rhgndf/hfsdr/art/art_export/cropped.png

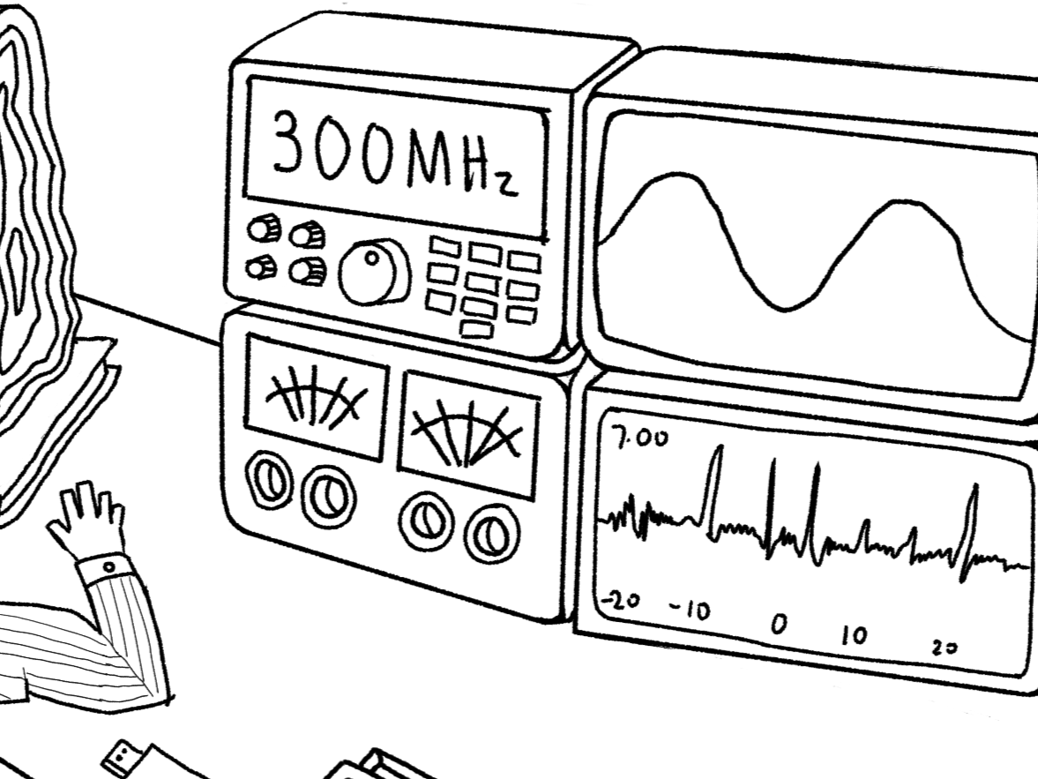
art/art_export/cropped.png
