rhgndf/hfsdr/hardware/screen docs/IMG_8584.JPG

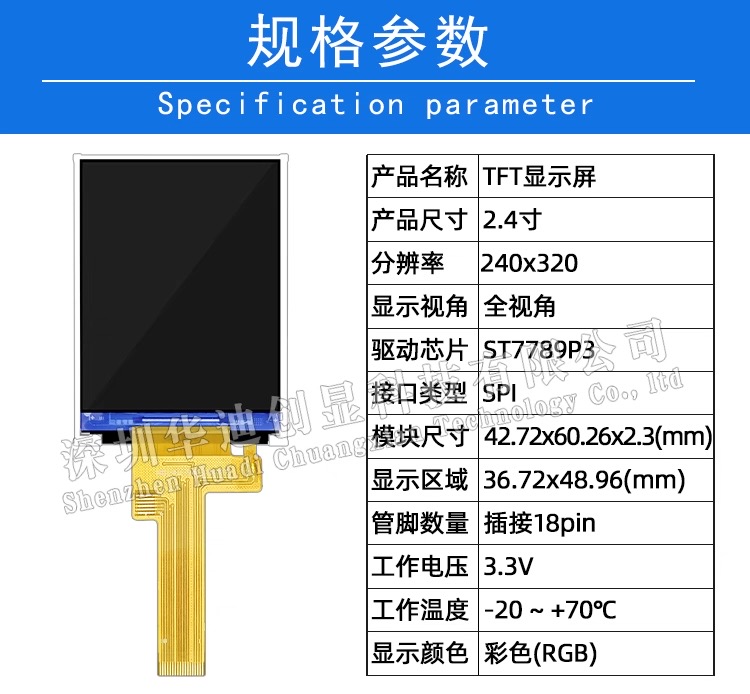
hardware/screen docs/IMG_8584.JPG
