rhgndf/hfsdr/hardware/screen docs/IMG_8585.JPG

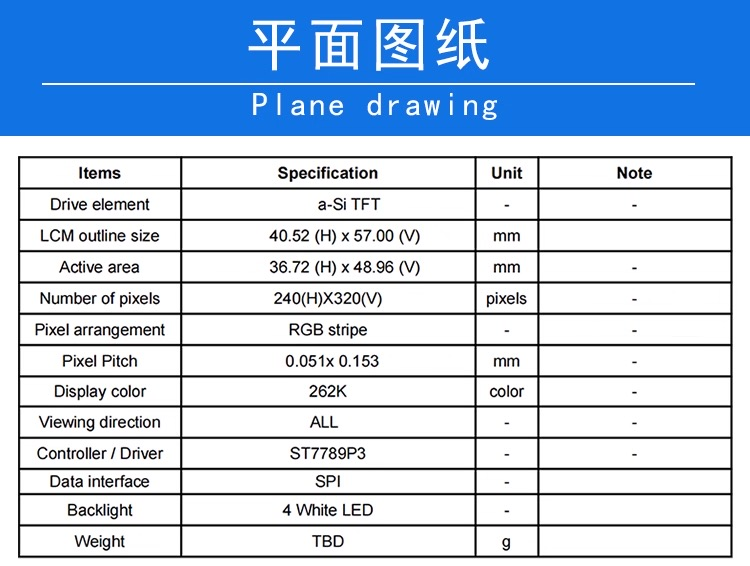
hardware/screen docs/IMG_8585.JPG
