rhgndf/hfsdr/hardware/screen docs/IMG_8586.JPG

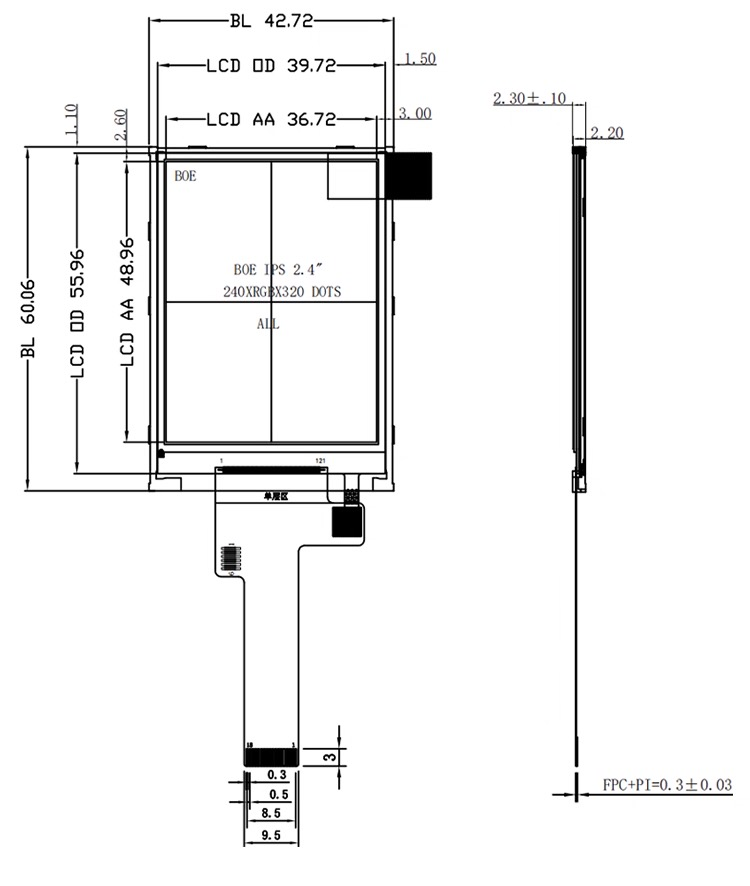
hardware/screen docs/IMG_8586.JPG
