rhgndf/hfsdr/hardware/screen docs/IMG_8587.JPG

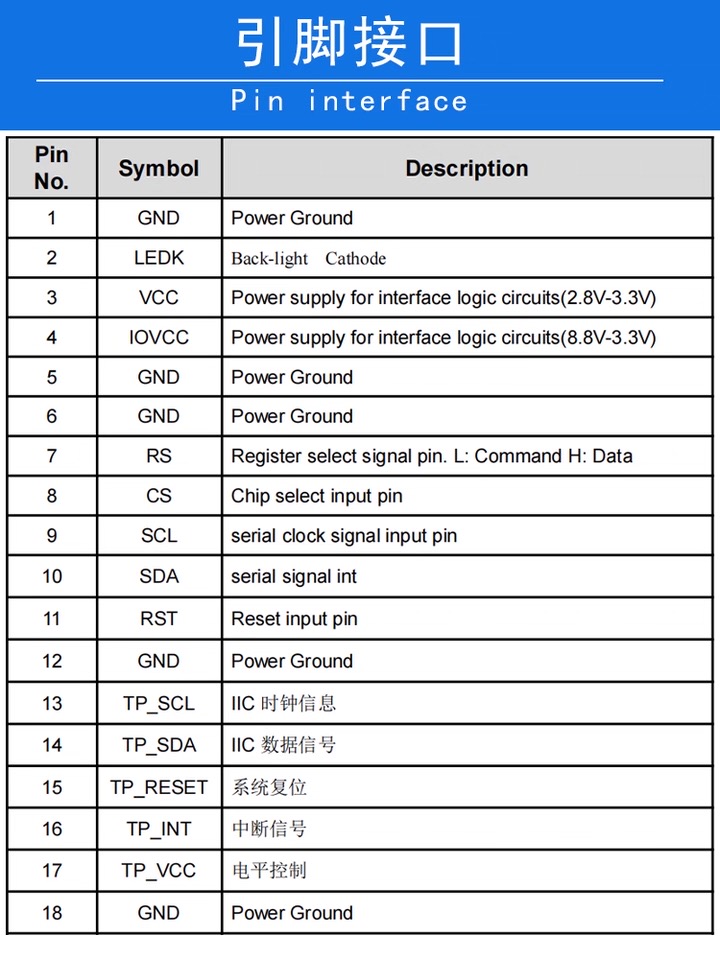
hardware/screen docs/IMG_8587.JPG
