rhgndf/hfsdr/hardware/screen docs/IMG_8588.JPG

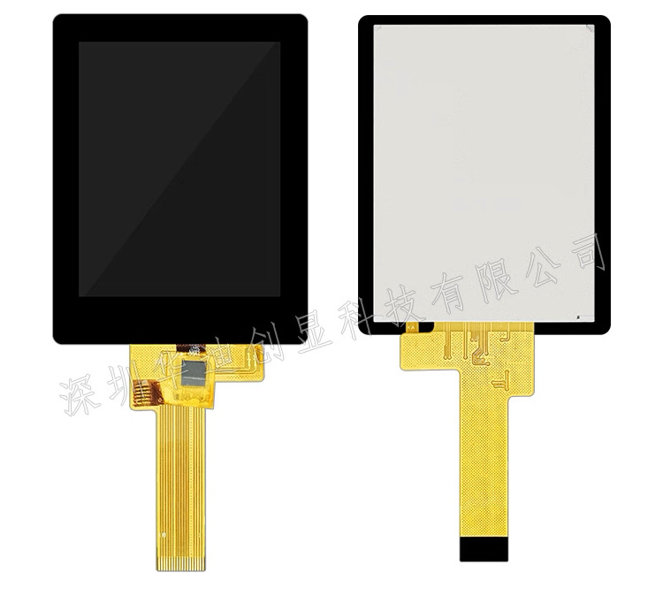
hardware/screen docs/IMG_8588.JPG
