rhgndf/hfsdr/ch32v305/src/tusb_config.h

/*
 * The MIT License (MIT)
 *
 * Copyright (c) 2020 Ha Thach (tinyusb.org)
 * Copyright (c) 2020 Jerzy Kasenberg
 *
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
 */

#ifndef TUSB_CONFIG_H_
#define TUSB_CONFIG_H_

#ifdef __cplusplus
extern "C" {
#endif

#include "usb_descriptors.h"

//--------------------------------------------------------------------+
// Board Specific Configuration
//--------------------------------------------------------------------+

// RHPort number used for device can be defined by board.mk, default to port 0
#ifndef BOARD_TUD_RHPORT
#define BOARD_TUD_RHPORT      0
#endif

// RHPort max operational speed can defined by board.mk
#ifndef BOARD_TUD_MAX_SPEED
#define BOARD_TUD_MAX_SPEED   OPT_MODE_DEFAULT_SPEED
#endif

//--------------------------------------------------------------------
// Common Configuration
//--------------------------------------------------------------------

// defined by compiler flags for flexibility
#ifndef CFG_TUSB_MCU
#error CFG_TUSB_MCU must be defined
#endif

#ifndef CFG_TUSB_OS
#define CFG_TUSB_OS           OPT_OS_FREERTOS
#endif

#ifndef CFG_TUSB_DEBUG
#define CFG_TUSB_DEBUG        0
#endif

// Enable Device stack
#define CFG_TUD_ENABLED       1

// Default is max speed that hardware controller could support with on-chip PHY
#define CFG_TUD_MAX_SPEED     BOARD_TUD_MAX_SPEED

/* USB DMA on some MCUs can only access a specific SRAM region with restriction on alignment.
 * Tinyusb use follows macros to declare transferring memory so that they can be put
 * into those specific section.
 * e.g
 * - CFG_TUSB_MEM SECTION : __attribute__ (( section(".usb_ram") ))
 * - CFG_TUSB_MEM_ALIGN   : __attribute__ ((aligned(4)))
 */
#ifndef CFG_TUSB_MEM_SECTION
#define CFG_TUSB_MEM_SECTION
#endif

#ifndef CFG_TUSB_MEM_ALIGN
#define CFG_TUSB_MEM_ALIGN        __attribute__ ((aligned(4)))
#endif

//--------------------------------------------------------------------
// DEVICE CONFIGURATION
//--------------------------------------------------------------------

#ifndef CFG_TUD_ENDPOINT0_SIZE
#define CFG_TUD_ENDPOINT0_SIZE    64
#endif

//------------- CLASS -------------//
#define CFG_TUD_CDC               1
#define CFG_TUD_MSC               0
#define CFG_TUD_HID               0
#define CFG_TUD_MIDI              0
#define CFG_TUD_AUDIO             1
#define CFG_TUD_VENDOR            1

//--------------------------------------------------------------------
// AUDIO CLASS DRIVER CONFIGURATION
//--------------------------------------------------------------------

// Single alternate streaming format: 24-bit samples in 32-bit slots.
#define CFG_TUD_AUDIO_FUNC_1_N_FORMATS                               1

// Audio format type I specifications
#define CFG_TUD_AUDIO_FUNC_1_MAX_SAMPLE_RATE                         192000
#define CFG_TUD_AUDIO_FUNC_1_N_CHANNELS_TX                           2
#define CFG_TUD_AUDIO_FUNC_1_N_CHANNELS_RX                           0

// 24-bit audio carried in 32-bit little-endian USB slots.
#define CFG_TUD_AUDIO_FUNC_1_FORMAT_1_N_BYTES_PER_SAMPLE_TX          4
#define CFG_TUD_AUDIO_FUNC_1_FORMAT_1_RESOLUTION_TX                  24

// EP and buffer size - for isochronous EP´s, the buffer and EP size are equal (different sizes would not make sense)
#define CFG_TUD_AUDIO_ENABLE_EP_IN                1

#define CFG_TUD_AUDIO_FUNC_1_FORMAT_1_EP_SZ_IN    TUD_AUDIO_EP_SIZE(TUD_OPT_HIGH_SPEED, CFG_TUD_AUDIO_FUNC_1_MAX_SAMPLE_RATE, CFG_TUD_AUDIO_FUNC_1_FORMAT_1_N_BYTES_PER_SAMPLE_TX, CFG_TUD_AUDIO_FUNC_1_N_CHANNELS_TX)

#define CFG_TUD_AUDIO_FUNC_1_EP_IN_SZ_MAX         CFG_TUD_AUDIO_FUNC_1_FORMAT_1_EP_SZ_IN
// Eight HS packets provide about 1 ms of buffering at the configured rate.
#define CFG_TUD_AUDIO_FUNC_1_EP_IN_SW_BUF_SZ      (TUD_OPT_HIGH_SPEED ? 8 : 4) * CFG_TUD_AUDIO_FUNC_1_EP_IN_SZ_MAX

#define CFG_TUD_AUDIO_ENABLE_EP_OUT               0

// CDC FIFO size of TX and RX
#define CFG_TUD_CDC_RX_BUFSIZE   (TUD_OPT_HIGH_SPEED ? 512 : 64)
#define CFG_TUD_CDC_TX_BUFSIZE   (TUD_OPT_HIGH_SPEED ? 256 : 64)

// CDC Endpoint transfer buffer size, more is faster
// Leave it as default size (512 for HS, 64 for FS) unless your host application
// is able to send ZLP (Zero Length Packet) to terminate transfer !
#define CFG_TUD_CDC_EP_BUFSIZE   (TUD_OPT_HIGH_SPEED ? 512 : 64)

// Vendor class endpoint and FIFO sizes must be >= endpoint packet size.
// With HS descriptors using 512-byte bulk endpoints, keep these at 512 for HS.
#define CFG_TUD_VENDOR_EPSIZE     (TUD_OPT_HIGH_SPEED ? 512 : 64)
#define CFG_TUD_VENDOR_RX_BUFSIZE 0 //(TUD_OPT_HIGH_SPEED ? 512 : 64)
#define CFG_TUD_VENDOR_TX_BUFSIZE 0 //(TUD_OPT_HIGH_SPEED ? 512 : 64)

#ifdef __cplusplus
}
#endif

#endif /* TUSB_CONFIG_H_ */
