rhgndf/hfsdr/ch32v305/src/hw/display/st7789.h

#ifndef __ST7789_H
#define __ST7789_H

#include "fonts.h"
#include "hw/pinout.h"

#include <stddef.h>
#include <stdint.h>

/* SPI: use spi_hw (SPI3). Init from ST7789_Init() via spi_hw_init(). */

/* Choose a display rotation you want to use: (0-3) */
#define ST7789_ROTATION 0
//#define ST7789_ROTATION 1
//#define ST7789_ROTATION 2
//#define ST7789_ROTATION 3


#if ST7789_ROTATION == 0
    #define ST7789_WIDTH 240
    #define ST7789_HEIGHT 320
    #define X_SHIFT 0
    #define Y_SHIFT 0
#endif

#if ST7789_ROTATION == 1
    #define ST7789_WIDTH 320
    #define ST7789_HEIGHT 240
    #define X_SHIFT 0
    #define Y_SHIFT 0
#endif

#if ST7789_ROTATION == 2
    #define ST7789_WIDTH 240
    #define ST7789_HEIGHT 320
    #define X_SHIFT 0
    #define Y_SHIFT 0
#endif

#if ST7789_ROTATION == 3
    #define ST7789_WIDTH 320
    #define ST7789_HEIGHT 240
    #define X_SHIFT 0
    #define Y_SHIFT 0
#endif

/**
 *Color of pen
 *If you want to use another color, you can choose one in RGB565 format.
 */

#define WHITE       0xFFFF
#define BLACK       0x0000
#define BLUE        0x001F
#define RED         0xF800
#define MAGENTA     0xF81F
#define GREEN       0x07E0
#define CYAN        0x7FFF
#define YELLOW      0xFFE0
#define GRAY        0X8430
#define BRED        0XF81F
#define GRED        0XFFE0
#define GBLUE       0X07FF
#define BROWN       0XBC40
#define BRRED       0XFC07
#define DARKBLUE    0X01CF
#define LIGHTBLUE   0X7D7C
#define GRAYBLUE    0X5458

#define LIGHTGREEN  0X841F
#define LGRAY       0XC618
#define LGRAYBLUE   0XA651
#define LBBLUE      0X2B12

/* Control Registers and constant codes */
#define ST7789_NOP     0x00
#define ST7789_SWRESET 0x01
#define ST7789_RDDID   0x04
#define ST7789_RDDST   0x09

#define ST7789_SLPIN   0x10
#define ST7789_SLPOUT  0x11
#define ST7789_PTLON   0x12
#define ST7789_NORON   0x13

#define ST7789_INVOFF  0x20
#define ST7789_INVON   0x21
#define ST7789_DISPOFF 0x28
#define ST7789_DISPON  0x29
#define ST7789_CASET   0x2A
#define ST7789_RASET   0x2B
#define ST7789_RAMWR   0x2C
#define ST7789_RAMRD   0x2E

#define ST7789_PTLAR   0x30
#define ST7789_VSCRDEF 0x33
#define ST7789_COLMOD  0x3A
#define ST7789_MADCTL  0x36
#define ST7789_VSCSAD  0x37
#define ST7789_VRHEN    0xC2
#define ST7789_VCMOFSET 0xC5

/**
 * Memory Data Access Control Register (0x36H)
 * MAP:     D7  D6  D5  D4  D3  D2  D1  D0
 * param:   MY  MX  MV  ML  RGB MH  -   -
 *
 */

/* Page Address Order ('0': Top to Bottom, '1': the opposite) */
#define ST7789_MADCTL_MY  0x80
/* Column Address Order ('0': Left to Right, '1': the opposite) */
#define ST7789_MADCTL_MX  0x40
/* Page/Column Order ('0' = Normal Mode, '1' = Reverse Mode) */
#define ST7789_MADCTL_MV  0x20
/* Line Address Order ('0' = LCD Refresh Top to Bottom, '1' = the opposite) */
#define ST7789_MADCTL_ML  0x10
/* RGB/BGR Order ('0' = RGB, '1' = BGR) */
#define ST7789_MADCTL_RGB 0x00

#define ST7789_RDID1   0xDA
#define ST7789_RDID2   0xDB
#define ST7789_RDID3   0xDC
#define ST7789_RDID4   0xDD

/* Advanced options */
#define ST7789_COLOR_MODE_16bit 0x55    //  RGB565 (16bit)
#define ST7789_COLOR_MODE_18bit 0x66    //  RGB666 (18bit)
#define ST7789_BITMAP_BUFFER_BYTES 128U

/* Basic operations — RST active-low (LOW = in reset, HIGH = run / released). */
#define ST7789_RST_Assert()  GPIO_WriteBit(ST7789_RST_GPIO_PORT, ST7789_RST_GPIO_PIN, Bit_RESET)
#define ST7789_RST_Release() GPIO_WriteBit(ST7789_RST_GPIO_PORT, ST7789_RST_GPIO_PIN, Bit_SET)

#define ABS(x) ((x) > 0 ? (x) : -(x))

#ifdef __cplusplus
extern "C" {
#endif

/* Basic functions. */
void ST7789_Init(void);
void ST7789_SetRotation(uint8_t m);
uint16_t ST7789_GetWidth(void);
uint16_t ST7789_GetHeight(void);
void ST7789_Fill_Color(uint16_t color);
void ST7789_DrawPixel(uint16_t x, uint16_t y, uint16_t color);
void ST7789_DrawColorLine(uint16_t x, uint16_t y, const uint16_t *colors, uint16_t width);
void ST7789_Fill(uint16_t xSta, uint16_t ySta, uint16_t xEnd, uint16_t yEnd, uint16_t color);
void ST7789_DrawPixel_4px(uint16_t x, uint16_t y, uint16_t color);
uint16_t ST7789_ScrollRows(uint16_t top, uint16_t bottom, int16_t rows);
void ST7789_VerticalScrollDisable(void);

/* Graphical functions. */
void ST7789_DrawLine(uint16_t x1, uint16_t y1, uint16_t x2, uint16_t y2, uint16_t color);
void ST7789_DrawLineFills(uint16_t x0, uint16_t y0, uint16_t x1, uint16_t y1, uint16_t color);
void ST7789_DrawRectangle(uint16_t x1, uint16_t y1, uint16_t x2, uint16_t y2, uint16_t color);
void ST7789_DrawCircle(uint16_t x0, uint16_t y0, uint8_t r, uint16_t color);
void ST7789_DrawImage(uint16_t x, uint16_t y, uint16_t w, uint16_t h, const uint16_t *data);
void ST7789_DrawBitmap1bpp(uint16_t x, uint16_t y, uint16_t w, uint16_t h,
                           const uint8_t *bits, uint16_t fg, uint16_t bg,
                           uint8_t *pixel_buf, size_t pixel_buf_size);
void ST7789_InvertColors(uint8_t invert);

/* Text functions. */
void ST7789_WriteChar(uint16_t x, uint16_t y, char ch, FontDef font, uint16_t color, uint16_t bgcolor);
void ST7789_WriteString(uint16_t x, uint16_t y, const char *str, FontDef font, uint16_t color, uint16_t bgcolor);
void ST7789_FillQuad(uint16_t x0, uint16_t y0, uint16_t x1, uint16_t y1,
                     uint16_t x2, uint16_t y2, uint16_t x3, uint16_t y3, uint16_t color);
void ST7789_BlitBitmap1bppRow(uint16_t x, uint16_t y, uint16_t w, uint16_t bitmap_w,
                              const uint8_t *bits, uint16_t fg, uint16_t bg);
void ST7789_WriteStringSlanted(int16_t x0, int16_t y0, const char *str, FontDef font, uint16_t color,
                               int16_t along_dx, int16_t along_dy, int16_t shear_num, int16_t shear_den);
void ST7789_WriteStringSlantedInQuad(int16_t x0, int16_t y0, const char *str, FontDef font, uint16_t color,
                                     int16_t along_dx, int16_t along_dy, int16_t shear_num, int16_t shear_den,
                                     uint16_t qx0, uint16_t qy0, uint16_t qx1, uint16_t qy1,
                                     uint16_t qx2, uint16_t qy2, uint16_t qx3, uint16_t qy3);

/* Extented Graphical functions. */
void ST7789_DrawFilledRectangle(uint16_t x, uint16_t y, uint16_t w, uint16_t h, uint16_t color);
void ST7789_DrawTriangle(uint16_t x1, uint16_t y1, uint16_t x2, uint16_t y2, uint16_t x3, uint16_t y3, uint16_t color);
void ST7789_DrawFilledTriangle(uint16_t x1, uint16_t y1, uint16_t x2, uint16_t y2, uint16_t x3, uint16_t y3, uint16_t color);
void ST7789_DrawFilledCircle(int16_t x0, int16_t y0, int16_t r, uint16_t color);

/* Command functions */
void ST7789_TearEffect(uint8_t tear);

/* Simple test function. */
void ST7789_Test(void);

#ifdef __cplusplus
}
#endif

#ifndef ST7789_ROTATION
    #error You should at least choose a display rotation!
#endif

#endif
