rhgndf/hfsdr/ch32v305/src/main.h

#ifndef MAIN_H
#define MAIN_H

#include "FreeRTOS.h"
#include "task.h"

#ifdef __cplusplus
extern "C" {
#endif

typedef enum
{
    HARDWARE_REV_UNKNOWN = 0,
    HARDWARE_REV_V1 = 1,
    HARDWARE_REV_V2 = 2,
} hardware_rev_t;

extern TaskHandle_t g_application_task_handle;

void detect_hardware_rev(void);
[[nodiscard]] hardware_rev_t get_hardware_rev(void);

#ifdef __cplusplus
}
#endif

#endif
