rhgndf/hfsdr/ch32v305/src/hw/usb.h

#ifndef USB_HW_H
#define USB_HW_H

#include <stddef.h>
#include <stdint.h>

#include "debug.h"

#define USB_HW_PLL_LOCK_STATE_SIZE 2U

void usb_task(void *parameters);
void usb_hw_vendor_write(volatile uint16_t const *src_words, size_t word_count);
uint32_t usb_hw_vendor_total_words(void);
uint32_t usb_hw_vendor_dropped_words(void);

uint32_t usb_send_data(uint8_t const *buffer, uint32_t len);
uint32_t usb_receive_data(uint8_t *buffer, uint32_t len);

ErrorStatus usb_hw_get_pll_lock(uint8_t *locked);

#endif
