rhgndf/hfsdr/ch32v305/src/ch32v30x_it.c

/********************************** (C) COPYRIGHT *******************************
* File Name          : ch32v30x_it.c
* Author             : WCH
* Version            : V1.0.0
* Date               : 2024/03/05
* Description        : Main Interrupt Service Routines.
*********************************************************************************
* Copyright (c) 2021 Nanjing Qinheng Microelectronics Co., Ltd.
* Attention: This software (modified or not) and binary are used for 
* microcontroller manufactured by Nanjing Qinheng Microelectronics.
*******************************************************************************/
#include "ch32v30x_it.h"
#include "freertos/port_isr.h"
#include "tusb.h"

void NMI_Handler(void) __attribute__((interrupt));
void HardFault_Handler(void) __attribute__((interrupt));

/*********************************************************************
 * @fn      NMI_Handler
 *
 * @brief   This function handles NMI exception.
 *
 * @return  none
 */
void NMI_Handler(void)
{
  while (1)
  {
  }
}

/*********************************************************************
 * @fn      HardFault_Handler
 *
 * @brief   This function handles Hard Fault exception.
 *
 * @return  none
 */
void HardFault_Handler(void)
{
  NVIC_SystemReset();
  while (1)
  {
  }
}

PORT_ISR_BODY(USBHS_IRQHandler)
{
  tud_int_handler(0);
}
