rhgndf/hfsdr/ch32v305/src/utils/dsp.h

#pragma once

#include <algorithm>
#include <bit>
#include <cstddef>
#include <cstdint>
#include <cstdlib>
#include <limits>
#include <utility>

template<typename T> struct WiderInt;
template<> struct WiderInt<int8_t>   { using type = int16_t;  };
template<> struct WiderInt<int16_t>  { using type = int32_t;  };
template<> struct WiderInt<int32_t>  { using type = int64_t;  };
template<> struct WiderInt<uint8_t>  { using type = uint16_t; };
template<> struct WiderInt<uint16_t> { using type = uint32_t; };
template<> struct WiderInt<uint32_t> { using type = uint64_t; };
template<typename T> using WiderInt_t = typename WiderInt<T>::type;

template<size_t QFRAC>
struct BiquadCoefficients
{
    int32_t b0;
    int32_t b1;
    int32_t b2;
    int32_t a1;
    int32_t a2;
};

template<size_t QFRAC>
struct BiquadState
{
    int32_t x1 = 0;
    int32_t x2 = 0;
    int32_t y1 = 0;
    int32_t y2 = 0;

    int32_t push(int32_t x, const BiquadCoefficients<QFRAC> &c)
    {
        int64_t acc = (int64_t)c.b0 * x
                    + (int64_t)c.b1 * x1
                    + (int64_t)c.b2 * x2
                    - (int64_t)c.a1 * y1
                    - (int64_t)c.a2 * y2;
        int32_t y = (int32_t)(acc >> QFRAC);
        x2 = x1;
        x1 = x;
        y2 = y1;
        y1 = y;
        return y;
    }

    void reset()
    {
        x1 = 0;
        x2 = 0;
        y1 = 0;
        y2 = 0;
    }
};

template<typename T, size_t N>
class CICFilter
{
    static_assert(N > 0 && (N & (N - 1)) == 0, "N must be a power of two");
    static constexpr size_t kShift = std::countr_zero(N);
    static constexpr size_t kMask = N - 1U;

    using Sum = WiderInt_t<T>;

    T hist[N] = {0};
    Sum sum = 0;
    size_t idx = 0U;

public:
    T push(T x)
    {
        T old = hist[idx];
        hist[idx] = x;
        idx = (idx + 1U) & kMask;
        sum += Sum(x) - old;
        return T(sum >> kShift);
    }

    void reset()
    {
        std::fill(hist, hist + N, 0);
        sum = 0;
        idx = 0U;
    }
};

template<typename T, size_t N, typename Sum = WiderInt_t<T>>
class CICComplexFilter
{
    static_assert(N > 0 && (N & (N - 1)) == 0, "N must be a power of two");
    static constexpr size_t kShift = std::countr_zero(N);
    static constexpr size_t kMask = N - 1U;

    /* Interleaved [i0,q0,i1,q1,...] so each tap fits in one cache line and the index/mask is shared. */
    T hist[2 * N] = {0};
    Sum sum_i = 0;
    Sum sum_q = 0;
    size_t idx = 0U;

public:
    std::pair<T, T> push(T i_now, T q_now)
    {
        size_t base = idx * 2U;
        T old_i = hist[base];
        T old_q = hist[base + 1U];
        hist[base] = i_now;
        hist[base + 1U] = q_now;
        idx = (idx + 1U) & kMask;
        sum_i += Sum(i_now) - old_i;
        sum_q += Sum(q_now) - old_q;
        return {T(sum_i >> kShift), T(sum_q >> kShift)};
    }

    void reset()
    {
        std::fill(hist, hist + 2 * N, 0);
        sum_i = 0;
        sum_q = 0;
        idx = 0U;
    }
};

/*
 * Single-pole IIR: y[n] = (1 - alpha) * x[n] + alpha * y[n-1], coefficients in QFRAC.
 * "One" saturates at type max for QFRAC == bit-width-1 since 2^(N-1) is unrepresentable in signed T.
 *
 * No saturating clamp on the output: with kOne == INT32_MAX (QFRAC=31), the
 * IIR is a strict convex combination — |state| <= max(|x|, |state_prev|), so
 * an input bounded by INT32_MAX keeps state bounded too. The atan2 output
 * feeding the FM path is in Q29 (< pi * 2^29 < 2^31), well within range.
 */
template<typename T, size_t QFRAC>
class SinglePoleIIR
{
    static_assert(QFRAC < sizeof(T) * 8, "QFRAC must be < bit-width of T");
    using Sum = WiderInt_t<T>;
    static constexpr T kOne = (QFRAC == sizeof(T) * 8 - 1)
                                ? std::numeric_limits<T>::max()
                                : T(T(1) << QFRAC);

    T state = 0;

public:
    T push(T x, T alpha)
    {
        Sum mixed = Sum(kOne - alpha) * x + Sum(alpha) * state;
        state = T(mixed >> QFRAC);
        return state;
    }

    T value() const { return state; }
    void seed(T x) { state = x; }
    void reset() { state = 0; }
};
